tomverbeure/logic_analyzer/board_setup_lvds.png

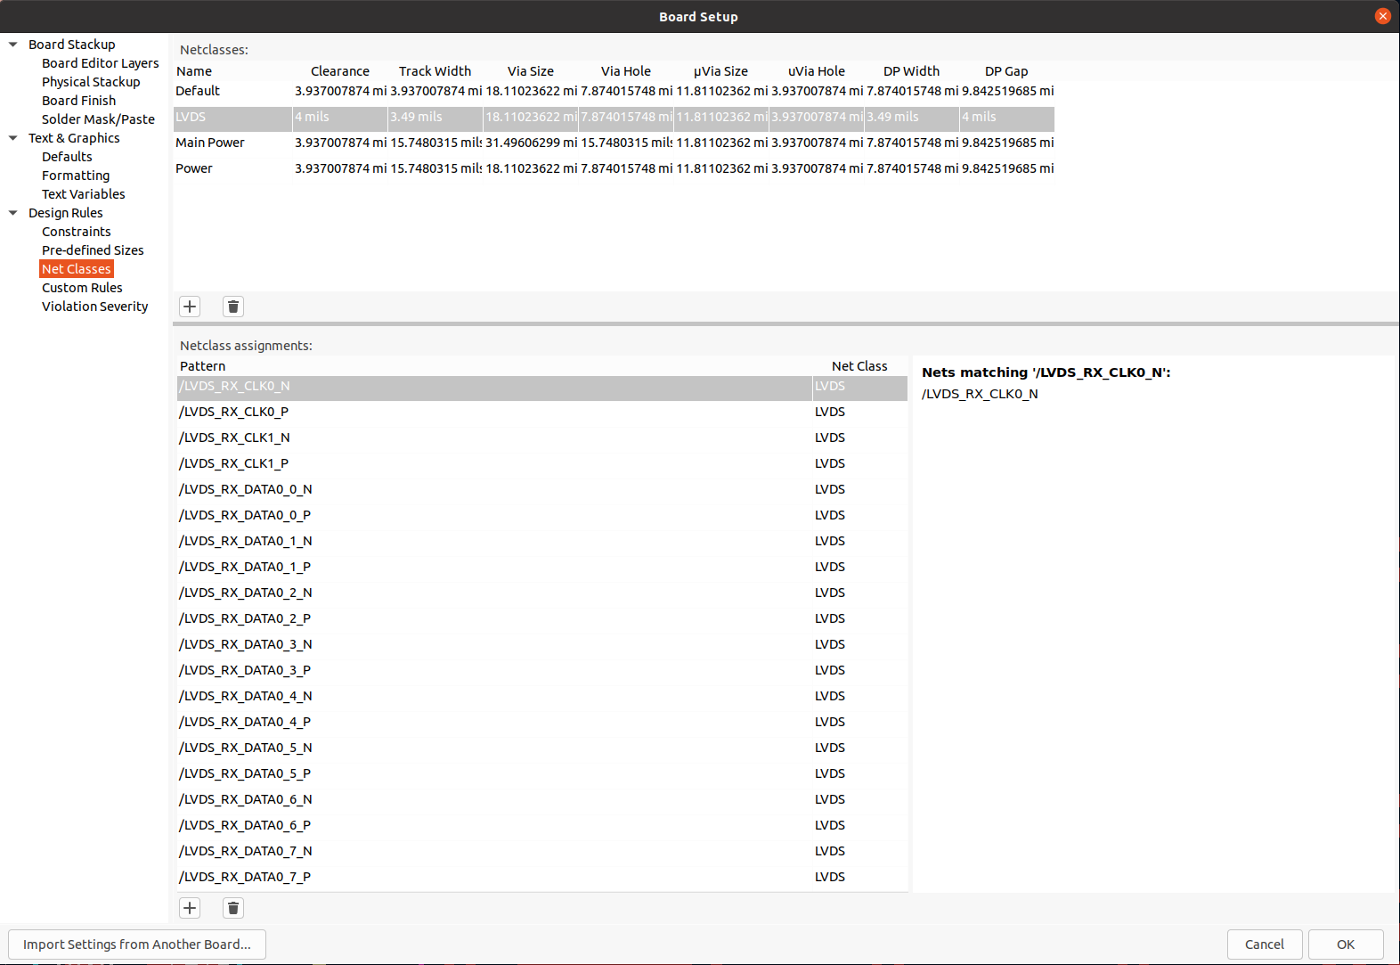
board_setup_lvds.png
