tomverbeure/logic_analyzer/ep2c5_experiments/results/lvttl3.0_50MHz.png

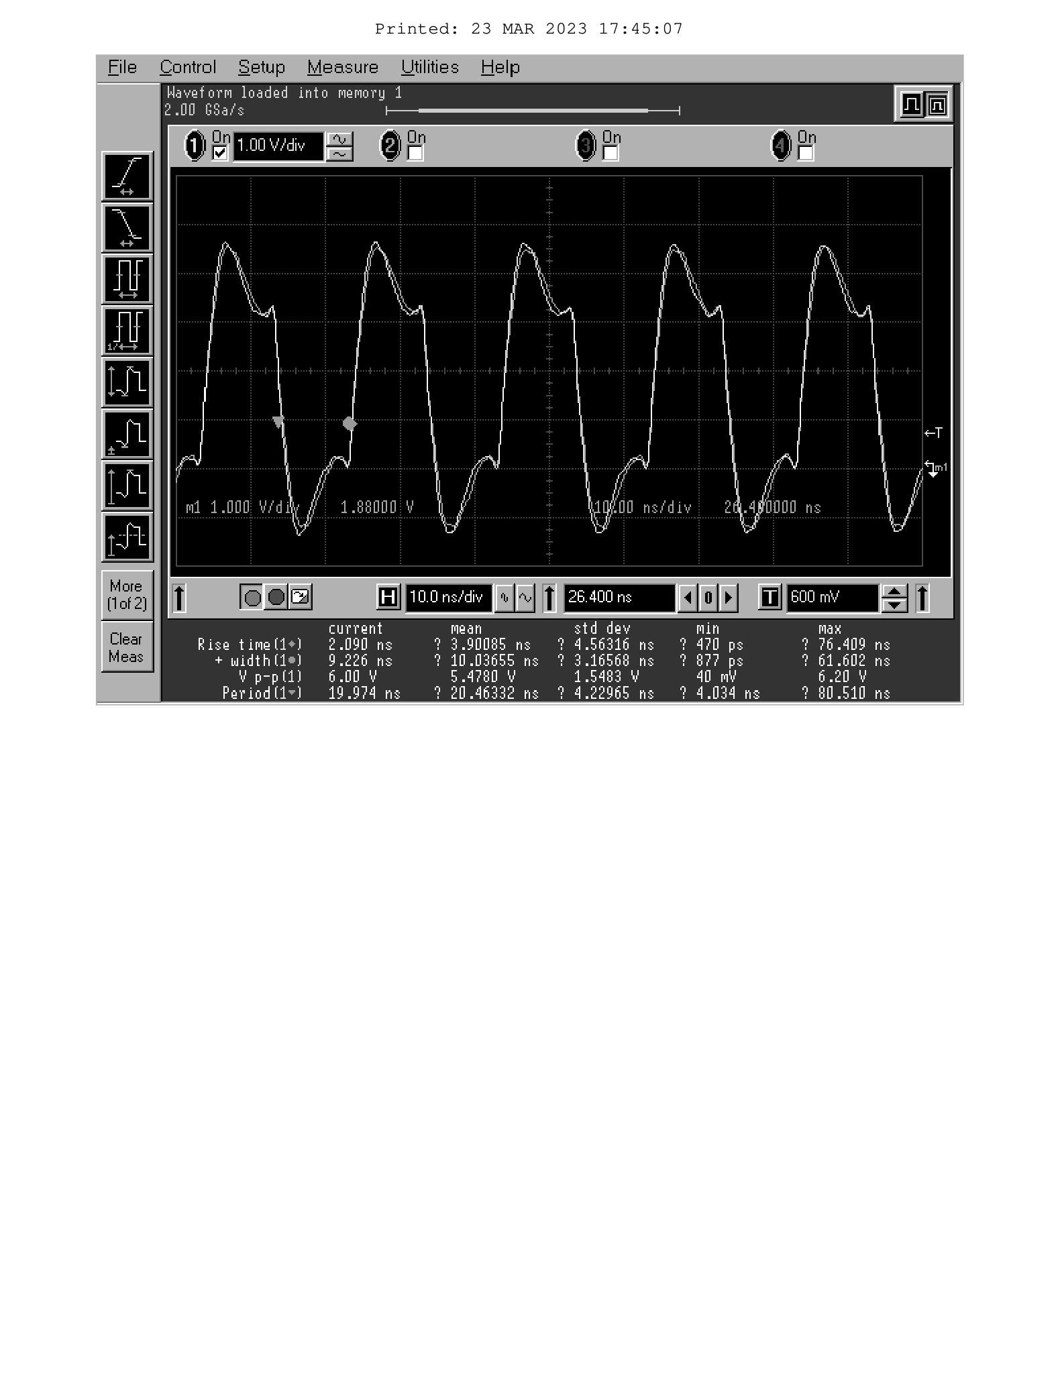
ep2c5_experiments/results/lvttl3.0_50MHz.png
