tomverbeure/logic_analyzer/ep2c35_la_mapping/models/lvds_rx_9chan_6x_inst.v

lvds_rx_9chan_6x	lvds_rx_9chan_6x_inst (
	.rx_data_align ( rx_data_align_sig ),
	.rx_in ( rx_in_sig ),
	.rx_inclock ( rx_inclock_sig ),
	.rx_locked ( rx_locked_sig ),
	.rx_out ( rx_out_sig ),
	.rx_outclock ( rx_outclock_sig )
	);
